Yassinebenj/GNSS_Dual_Band_Front-End/Honorable Mention Certificate.jpeg

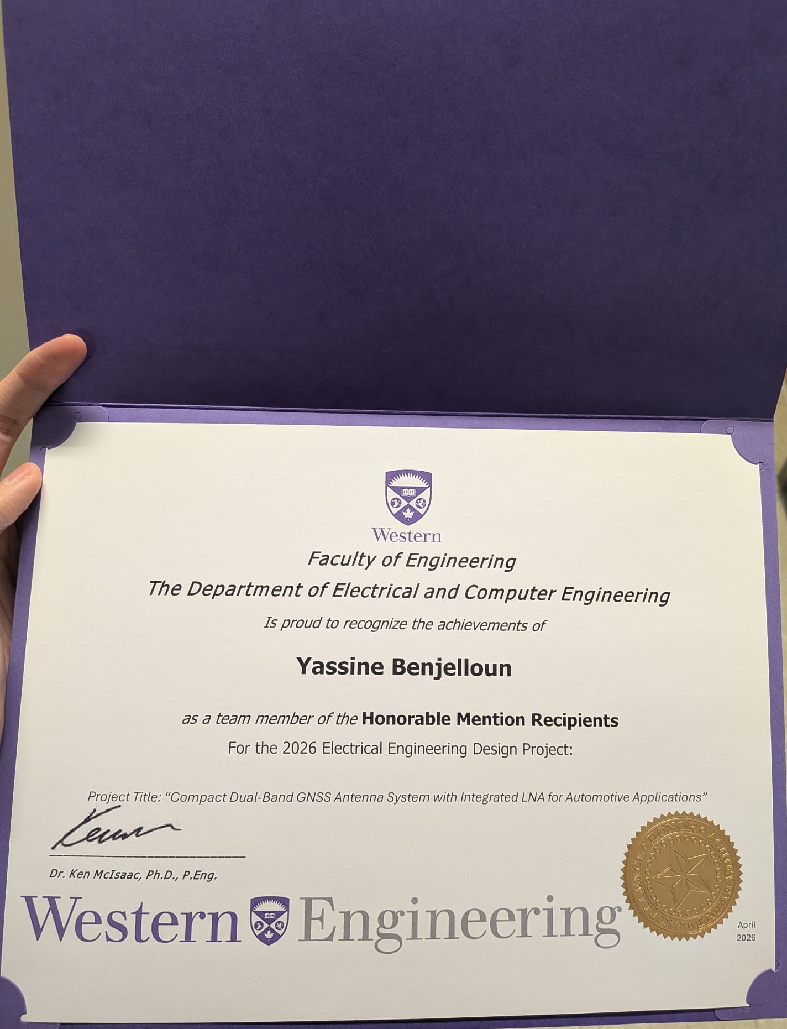
Honorable Mention Certificate.jpeg
