Yassinebenj/GNSS_Dual_Band_Front-End/Layouts/L1 PCB Antenna Layout.png

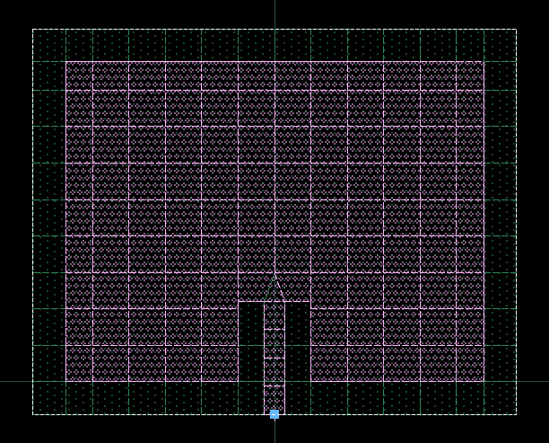
Layouts/L1 PCB Antenna Layout.png
