Yassinebenj/GNSS_Dual_Band_Front-End/Layouts/L5 PCB Antenna Layout.png

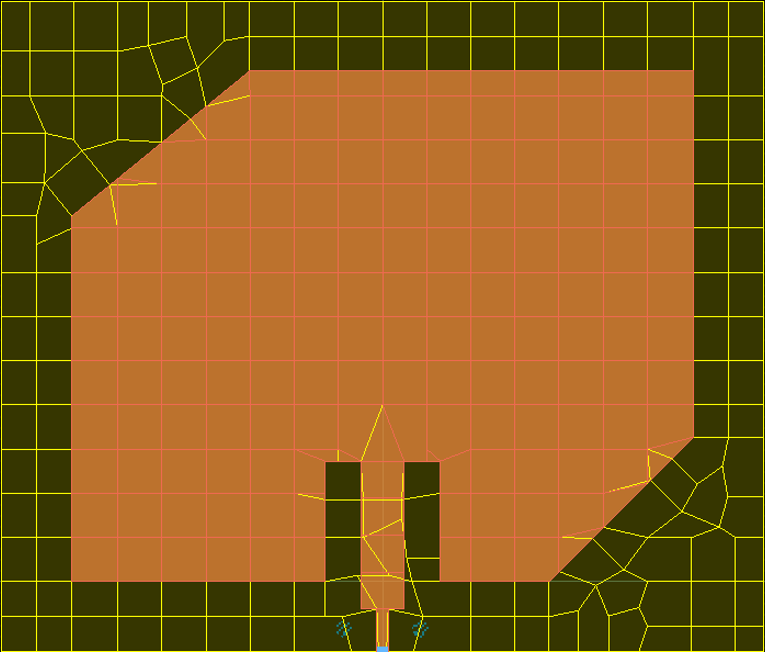
Layouts/L5 PCB Antenna Layout.png
