Yassinebenj/GNSS_Dual_Band_Front-End/Layouts/PCB Stackup.png

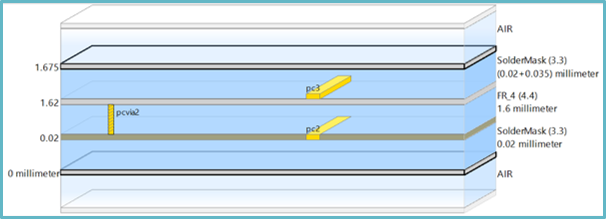
Layouts/PCB Stackup.png
