Yassinebenj/GNSS_Dual_Band_Front-End/Layouts/Signal Processing PCB Layout.png

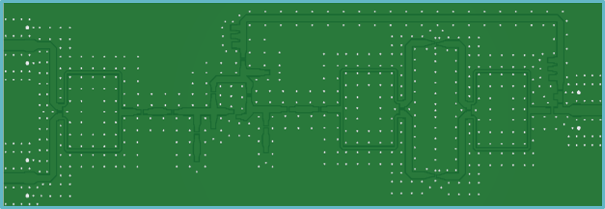
Layouts/Signal Processing PCB Layout.png
