Yassinebenj/GNSS_Dual_Band_Front-End/Layouts/Wilkinson Divider Layout.png

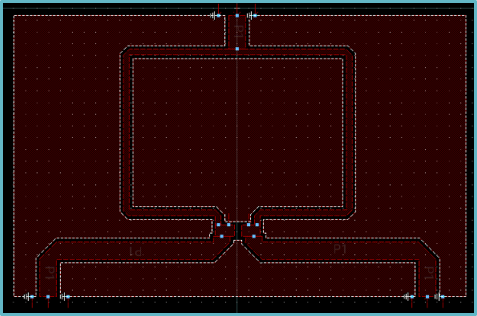
Layouts/Wilkinson Divider Layout.png
