Yassinebenj/GNSS_Dual_Band_Front-End/Schematics/Bias Tee.png

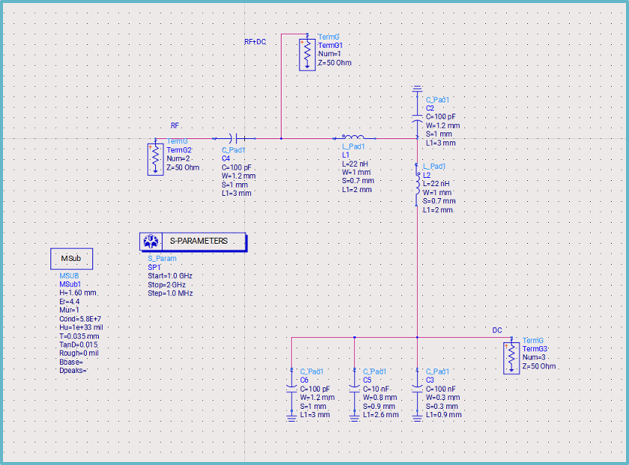
Schematics/Bias Tee.png
