Yassinebenj/GNSS_Dual_Band_Front-End/Schematics/L1 Band-Pass Filter.png

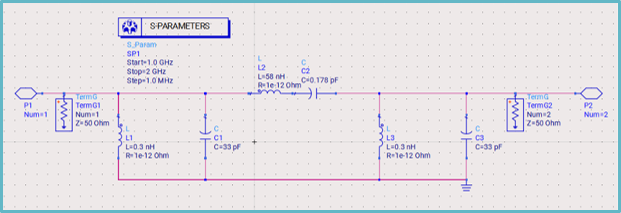
Schematics/L1 Band-Pass Filter.png
