Yassinebenj/GNSS_Dual_Band_Front-End/Schematics/Selected LNA.png

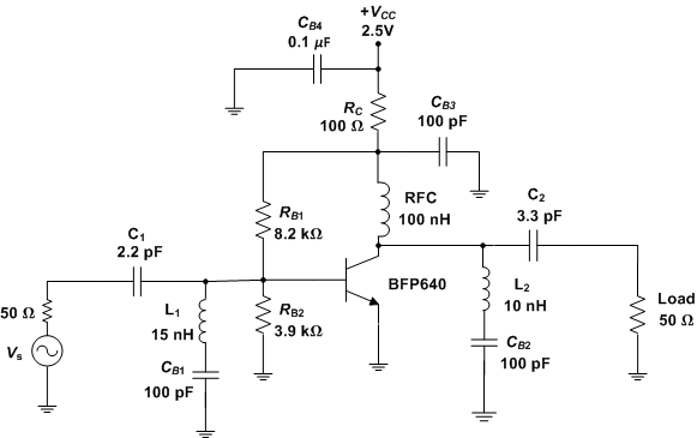
Schematics/Selected LNA.png
