Yassinebenj/GNSS_Dual_Band_Front-End/Simulation Results/Band-Pass Filters Results.png

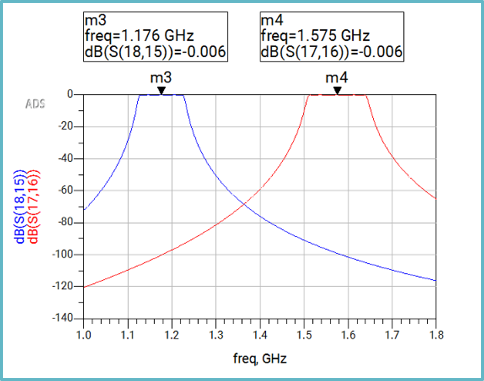
Simulation Results/Band-Pass Filters Results.png
