Yassinebenj/GNSS_Dual_Band_Front-End/Simulation Results/L1 Current Distribution.png

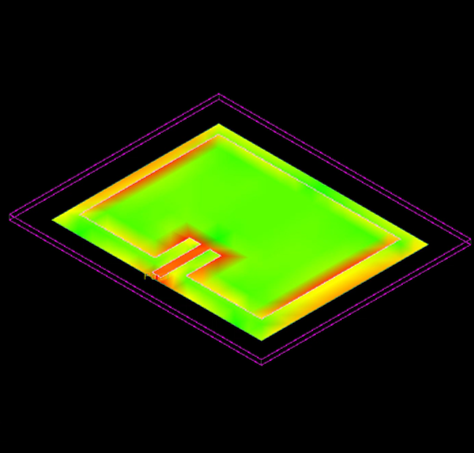
Simulation Results/L1 Current Distribution.png
