Yassinebenj/GNSS_Dual_Band_Front-End/Simulation Results/L1 Far Fields Visualization.png

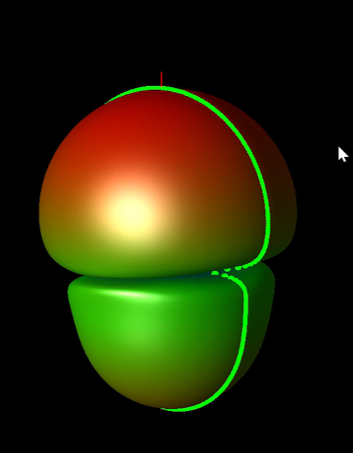
Simulation Results/L1 Far Fields Visualization.png
