Yassinebenj/GNSS_Dual_Band_Front-End/Simulation Results/L5 Current Distribution.png

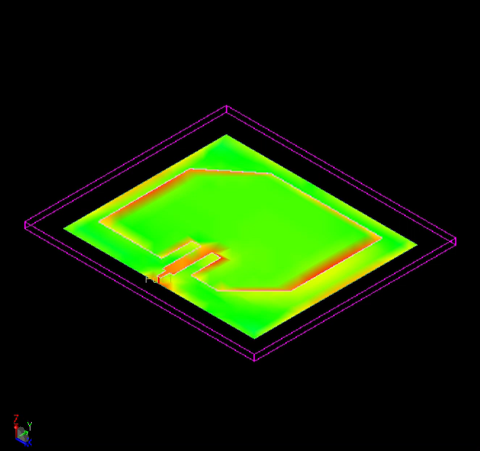
Simulation Results/L5 Current Distribution.png
