Yassinebenj/GNSS_Dual_Band_Front-End/Simulation Results/L5 Far Field Visualization.png

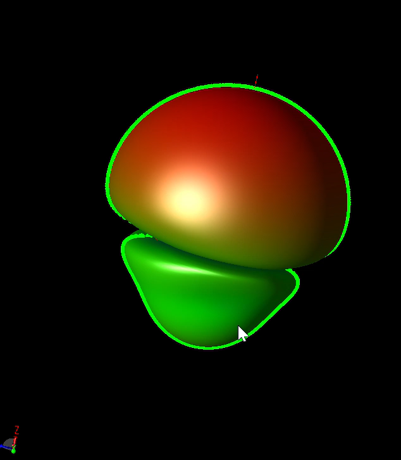
Simulation Results/L5 Far Field Visualization.png
