Yassinebenj/GNSS_Dual_Band_Front-End/Simulation Results/L5 Return Loss Results.png

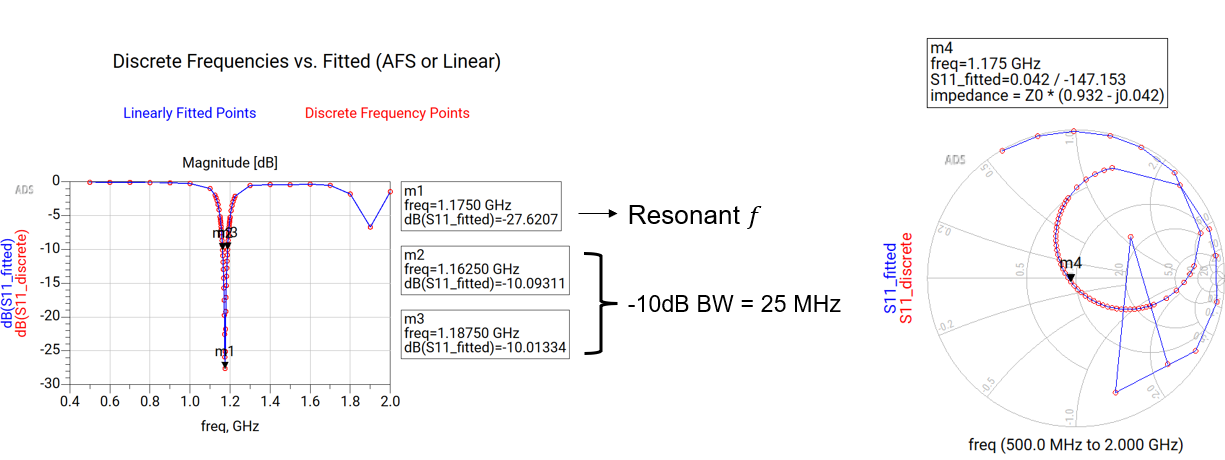
Simulation Results/L5 Return Loss Results.png
