Yassinebenj/GNSS_Dual_Band_Front-End/Simulation Results/LNA Simulation Results.png

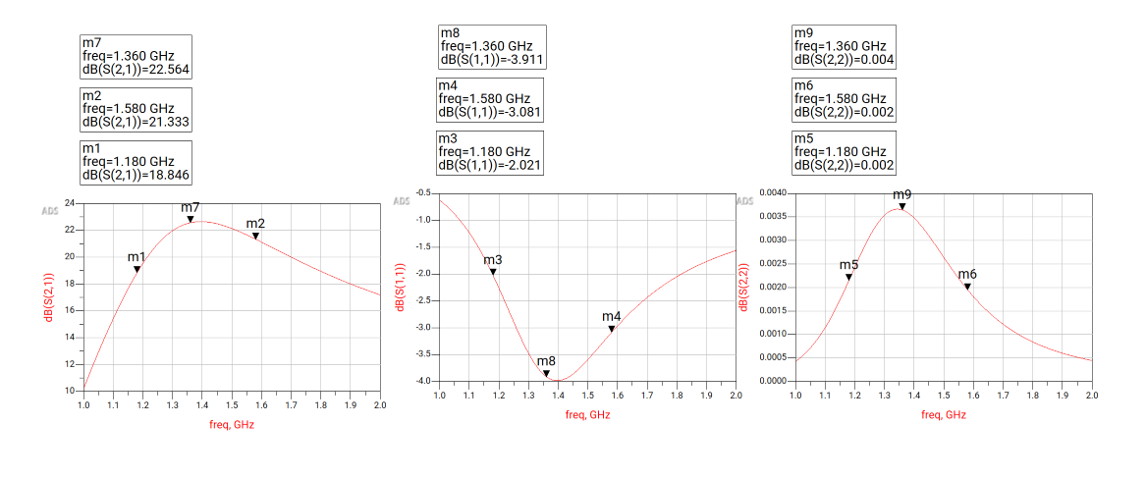
Simulation Results/LNA Simulation Results.png
