Yassinebenj/GNSS_Dual_Band_Front-End/Simulation Results/System Results.png

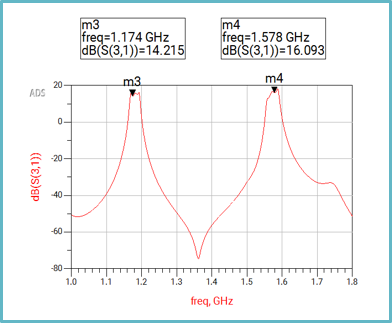
Simulation Results/System Results.png
