Yassinebenj/GNSS_Dual_Band_Front-End/Simulation Results/Wilkinson Divider Return Loss Results.png

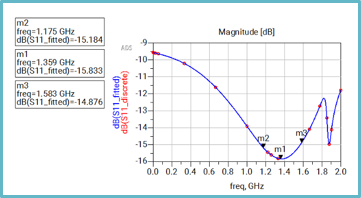
Simulation Results/Wilkinson Divider Return Loss Results.png
